mackelec/arduLCDkeypad/SRC_arduLCDkeypad/LLCD_090_notes.ino

//    https://github.com/MCUdude/MiniCore
//    https://www.arduino.cc/en/Tutorial/ArduinoISP
//    http://www.gammon.com.au/breadboard
//    https://github.com/kroimon/Arduino-SerialCommand   https://github.com/scogswell/ArduinoSerialCommand
//    https://github.com/SMFSW/Queue/blob/master/src/cppQueue.h
//    http://pighixxx.com/nanopdf.pdf
